paulscherrerinstitute/LedStripI2c/hdl/LedStripController.vhd

library ieee;
use     ieee.std_logic_1164.all;
use     ieee.numeric_std.all;

use     work.MpcI2cSequencerPkg.all;

entity LedStripController is
  generic (
    -- SCL freq. is frequency of 'clk' divided by 4*FDR_RATIO (selected by FDRVAL)
    I2C_FDRVAL_G : std_logic_vector(7 downto 0);
    I2C_ADDR_R_G : std_logic_vector(6 downto 0) := "0000101";
    I2C_ADDR_L_G : std_logic_vector(6 downto 0) := "1101001";
    -- Debouncer (synchronizers and debounce delays effectively slower the max. SCL rate!)
    -- synchronization stages in the SDA/SCL input debouncer
    DBNCE_SYNC_G : natural range 0 to 3         := 3;
    -- for how many cycles to debounce the incoming SDA/SCL signals
    DBNCE_CYCL_G : natural                      := 10
  );
  port (
    clk          : in  std_logic;
    rst          : in  std_logic;

    strobe       : in  std_logic;
    pulseid      : in  std_logic_vector(63 downto 0);
    pwm          : in  std_logic_vector( 7 downto 0) := x"ff"; -- pwm brightness control
    iref         : in  std_logic_vector( 7 downto 0) := x"80"; -- analog brightness control
    grayCode     : in  std_logic;
    busy         : out std_logic;

    fdrRegValid  : in  std_logic                     := '0';
    fdrRegData   : in  std_logic_vector( 7 downto 0) := I2C_FDRVAL_G;

    malErrors    : out std_logic_vector(31 downto 0);
    nakErrors    : out std_logic_vector(31 downto 0);
    rbkErrors    : out std_logic_vector(31 downto 0);

    sdaDir       : out std_logic;
    sdaOut       : out std_logic;
    sdaInp       : in  std_logic;
    sclOut       : out std_logic;
    sclInp       : in  std_logic;

    dbgState     : out std_logic_vector(19 downto 0)
  );
end entity LedStripController;

architecture rtl of LedStripController is

  constant NUM_CTRL_C                : natural := 2;
  constant NUM_LEDS_PER_CONTROLLER_C : natural := 16;
  constant NUM_LEDS_C                : natural := NUM_CTRL_C * NUM_LEDS_PER_CONTROLLER_C;

  subtype  Slv8           is std_logic_vector( 7 downto 0);
  subtype  U8             is unsigned        ( 7 downto 0);
  subtype  Slv32          is std_logic_vector(31 downto 0);
  subtype  U32            is unsigned        (31 downto 0);
  subtype  PidType        is std_logic_vector(NUM_LEDS_C - 1 downto 0);

  subtype  I2cAddrType    is std_logic_vector( 6 downto 0);

  constant SL_ONE_C        : std_logic := '1';

  -- addresses in the pca9955B
  -- bit 7 lets address auto-increment
  constant LED_MODE_ADDR_C : U8 := x"82";
  constant LED_IREF_ADDR_C : U8 := x"88";
  constant LED_IPWM_ADDR_C : U8 := x"98";

  constant SHOW_PID_PROG_C : MpcI2cSequenceArray := (
    SEQ_NORM & I2C_ADDR_R_G & "0", -- first item generates a start condition if bus is not owned
    SEQ_NORM & Slv8(LED_MODE_ADDR_C),
    SEQ_NORM & x"00",              -- Four bytes with control data
    SEQ_NORM & x"00",              -- 
    SEQ_NORM & x"00",              -- 
    SEQ_NORM & x"00",              -- 
    SEQ_RSRT & I2C_ADDR_L_G & "0", -- RESTART with second controller
    SEQ_NORM & Slv8(LED_MODE_ADDR_C),
    SEQ_NORM & x"00",              -- Four bytes with control data
    SEQ_NORM & x"00",              -- 
    SEQ_NORM & x"00",              -- 
    SEQ_STOP & x"00"               -- STOP updates BOTH controllers' displays
  );

  constant READBACK_PID_AND_SEND_BYTE_PROG_C : MpcI2cSequenceArray := (
    SEQ_NORM & I2C_ADDR_R_G & "0",
    SEQ_NORM & Slv8(LED_MODE_ADDR_C),
    SEQ_RSRT & I2C_ADDR_R_G & "1",
    SEQ_NORM & x"03",              -- read-back 4 bytes
    SEQ_RSRT & I2C_ADDR_L_G & "0",
    SEQ_NORM & Slv8(LED_MODE_ADDR_C),
    SEQ_RSRT & I2C_ADDR_L_G & "1",
    SEQ_NORM & x"03",              -- read-back 4 bytes
    SEQ_RSRT & I2C_ADDR_R_G & "0", -- i2c address
    SEQ_NORM & Slv8(LED_IREF_ADDR_C),
    SEQ_STOP & x"00"               -- data
  );

  constant PROGS_INIT_C       : MpcI2cSequenceArray := (
    SHOW_PID_PROG_C &
    READBACK_PID_AND_SEND_BYTE_PROG_C
  );

  constant PROGS_LENGTH_C     : natural := PROGS_INIT_C'length;

  signal   programs           : MpcI2cSequenceArray(PROGS_INIT_C'range) := PROGS_INIT_C;

  subtype  PCType            is natural range 0 to PROGS_LENGTH_C - 1;

  constant SHOW_PID_ADDR_C    : natural := 0;
  constant RBCK_PID_ADDR_C    : natural := SHOW_PID_PROG_C'length;

  constant CTL_OFF_C          : natural := 2; -- offset of first control byte (LHS controller)
  constant CTL_NBYTES_C       : natural := 4; -- 4 control bytes control 16 LEDs

  constant BRI_I2C_OFF_C      : natural := 0 + 8;
  constant BRI_ADR_OFF_C      : natural := 1 + 8;
  constant BRI_VAL_OFF_C      : natural := 2 + 8;

  constant PWM_INI_C          : Slv8 := x"FF";
  constant IREF_INI_C         : Slv8 := x"80";

  subtype  RbkCountType   is natural range 0 to CTL_NBYTES_C * NUM_CTRL_C;

  type StateType is (WAIT_READY, IDLE, START_SHOW_PID, START_SET_BRIGHTNESS);

  type RegType is record
    progPtr     :  PCType;
    progValid   :  std_logic;
    state       :  StateType;
    briRight    :  boolean;
    briI2c      :  I2cAddrType;
    pwm         :  Slv8;
    iref        :  Slv8;
    briAddr     :  U8;
    briData     :  Slv8;
    rbkCount    :  RbkCountType;
    rbkErrors   :  U32;
  end record RegType;

  constant REG_INIT_C : RegType := (
    progPtr     => SHOW_PID_ADDR_C,
    progValid   => '0',
    state       => WAIT_READY,
    briRight    => true,
    briI2c      => I2C_ADDR_R_G,
    pwm         => PWM_INI_C,
    iref        => IREF_INI_C,
    briAddr     => LED_IREF_ADDR_C,
    briData     => IREF_INI_C,
    rbkCount    => RbkCountType'high,
    rbkErrors   => (others => '0')
  );

  procedure setPID(
    signal   prg  : inout MpcI2cSequenceArray;
    constant off  : natural;
    constant pid  : PidType;
    constant gray : std_logic
  ) is
    variable v : PidType;
  begin
    v := pid;
    if ( gray = '1' ) then
      v := (pid xor ('0' & pid(pid'left downto pid'right + 1) ));
    end if;
    -- each bit in the PID vector is represented by two bits in the control words: '0' => "00", '1' => "10"
    -- (see PCA9955 datasheet)
    for i in 0 to NUM_CTRL_C - 1 loop
      for j in 0 to CTL_NBYTES_C - 1 loop
        for k in 0 to 3 loop
          prg( off + CTL_OFF_C + (CTL_OFF_C + CTL_NBYTES_C) * i + j )(2*k + 1) <= v( i * NUM_LEDS_C/NUM_CTRL_C + j*4 + k );
        end loop;
      end loop;
    end loop;
  end procedure setPID;

  procedure nextBriMux(variable rg : inout RegType) is
  begin
    rg.briAddr := rg.briAddr + 1;
    if ( rg.briAddr = LED_IPWM_ADDR_C ) then
      rg.briData := rg.pwm; 
    elsif ( rg.briAddr = LED_IPWM_ADDR_C + NUM_LEDS_PER_CONTROLLER_C ) then
      rg.briAddr := LED_IREF_ADDR_C;
      rg.briData := rg.iref;
      if ( rg.briRight ) then
        rg.briI2c := I2C_ADDR_L_G;
      else
        rg.briI2c := I2C_ADDR_R_G;
      end if;
      rg.briRight :=  not rg.briRight;
    end if;
  end procedure nextBriMux;

  procedure setSendByte(
    signal   prg     : inout MpcI2cSequenceArray;
    constant off     : natural;
    constant i2caddr : I2cAddrType;
    constant waddr   : U8;
    constant wdata   : Slv8
  ) is
  begin
    prg( off + BRI_I2C_OFF_C )(7 downto 1) <= i2caddr;
    prg( off + BRI_ADR_OFF_C )(7 downto 0) <= Slv8(waddr);
    prg( off + BRI_VAL_OFF_C )(7 downto 0) <= wdata;
  end procedure setSendByte;

  signal progReady      : std_logic;

  signal r              : RegType := REG_INIT_C;
  signal rin            : RegType;

  signal sclInpFiltered : std_logic;
  signal sdaInpFiltered : std_logic;

  signal readbackData   : std_logic_vector(7 downto 0);
  signal readbackValid  : std_logic;
  signal progError      : std_logic;

  signal offDbg         : natural;
  signal rboffDbg       : std_logic_vector(7 downto 0);

begin

  P_MEM  : process( clk ) is
  begin
    if ( rising_edge( clk ) ) then
      if ( rst = '1' ) then
        programs <= PROGS_INIT_C;
      else
        if ( strobe = '1' and (r.state = IDLE) ) then
          setPID(programs, SHOW_PID_ADDR_C, pulseid(PidType'range), gray => grayCode);
          setSendByte(programs, RBCK_PID_ADDR_C, r.briI2c, r.briAddr, r.briData);
        end if;
      end if;
    end if;
  end process P_MEM;

  P_COMB : process(r, strobe, pulseid, pwm, iref, progReady, readbackValid, readbackData) is
    variable v     : RegType;
    variable off   : PCType;
  begin
    v          := r;
    if ( readbackValid = '1' ) then
      -- incur a bound-check failure during simulation since the combinatorial
      -- process increments v.rbkCount if not checked
      if ( r.rbkCount < RbkCountType'high ) then
        v.rbkCount := r.rbkCount + 1;
      end if;
      off := SHOW_PID_ADDR_C + CTL_OFF_C + r.rbkCount;
      if ( r.rbkCount >= CTL_NBYTES_C ) then
        off := off + CTL_OFF_C;
      end if;
      offDbg <= off;
      rboffDbg <= programs(off)(7 downto 0);
      if ( readbackData /= programs(off)(7 downto 0) ) then
        v.rbkErrors := r.rbkErrors + 1;
      end if;
    end if;
    case ( r.state ) is
      when WAIT_READY =>
        if ( progReady = '1' ) then
          v.state     := IDLE;
          v.rbkErrors := r.rbkErrors + (RbkCountType'high - r.rbkCount);
          v.rbkCount  := 0;
        end if;

      when IDLE =>
        if ( strobe = '1' ) then
          v.state     := START_SHOW_PID;
          v.progValid := '1';
          v.iref      := iref;
          v.pwm       := pwm;
        end if;

      when START_SHOW_PID =>
        if ( (r.progValid and progReady) = '1' ) then
          v.state   := START_SET_BRIGHTNESS;
          v.progPtr := RBCK_PID_ADDR_C;
        end if;

      when START_SET_BRIGHTNESS =>
        if ( (r.progValid and progReady) = '1' ) then
          v.state     := WAIT_READY;
          v.progPtr   := SHOW_PID_ADDR_C;
          v.progValid := '0';
          nextBriMux( v );
        end if;

    end case;
    rin        <= v;
  end process P_COMB;

  P_SEQ : process ( clk ) is
  begin
    if ( rising_edge( clk ) ) then
      if ( rst = '1' ) then
        r <= REG_INIT_C;
      else
        r <= rin;
      end if;
    end if;
  end process P_SEQ;

  U_DebounceSCL : entity work.InpDebouncer
    generic map (
      SYNC_STAGES_G => DBNCE_SYNC_G,
      LOHI_STABLE_G => DBNCE_CYCL_G,
      HILO_STABLE_G => DBNCE_CYCL_G,
      RESET_STATE_G => SL_ONE_C
    )
    port map (
      clk           => clk,
      rst           => rst,
      dataIn        => sclInp,
      dataOut       => sclInpFiltered
    );

  U_DebounceSDA : entity work.InpDebouncer
    generic map (
      SYNC_STAGES_G => DBNCE_SYNC_G,
      LOHI_STABLE_G => DBNCE_CYCL_G,
      HILO_STABLE_G => DBNCE_CYCL_G,
      RESET_STATE_G => SL_ONE_C
    )
    port map (
      clk           => clk,
      rst           => rst,
      dataIn        => sdaInp,
      dataOut       => sdaInpFiltered
    );

  U_Controller : entity work.MpcI2cSequencer
    generic map (
      MEM_DEPTH_G   => PROGS_LENGTH_C,
      I2C_FDRVAL_G  => I2C_FDRVAL_G
    )
    port map (
      clk           => clk,
      rst           => rst,

      memory        => programs,
      memPtr        => r.progPtr,
      memPtrValid   => r.progValid,
      memPtrReady   => progReady,

      progError     => progError,

      fdrRegValid   => fdrRegValid,
      fdrRegData    => fdrRegData,

      malErrors     => malErrors,
      nakErrors     => nakErrors,

      readData      => readbackData,
      readValid     => readbackValid,

      sdaDir        => sdaDir,
      sdaOut        => sdaOut,
      sdaInp        => sdaInpFiltered,
      sclOut        => sclOut,
      sclInp        => sclInpFiltered,

      dbgState      => dbgState(15 downto 0)
    );

  dbgState(18 downto 16) <= std_logic_vector( to_unsigned( StateType'pos( r.state ), 3 ) );
  dbgState(19)           <= '0';

  busy                   <= '1' when (r.state /= IDLE) else '0';

  rbkErrors              <= std_logic_vector(r.rbkErrors);
 
end architecture rtl;
